dierickdie/lucy/01.1_non-snap-off/02_ori_top_plate.png

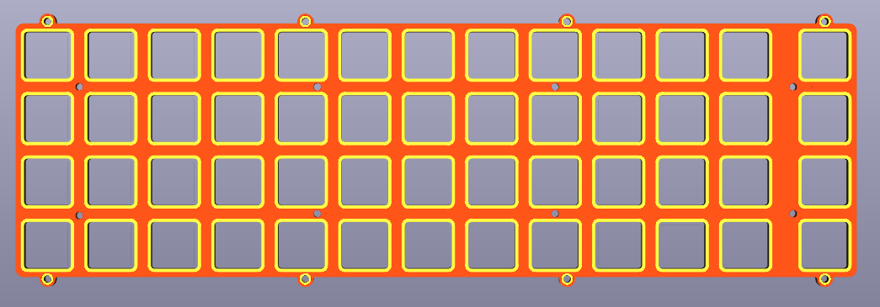
01.1_non-snap-off/02_ori_top_plate.png
