dierickdie/lucy/01_pcb/3.0-QFN-0603/footprints/AcheronLibrary-master/graphics/e6c1209rgb.png

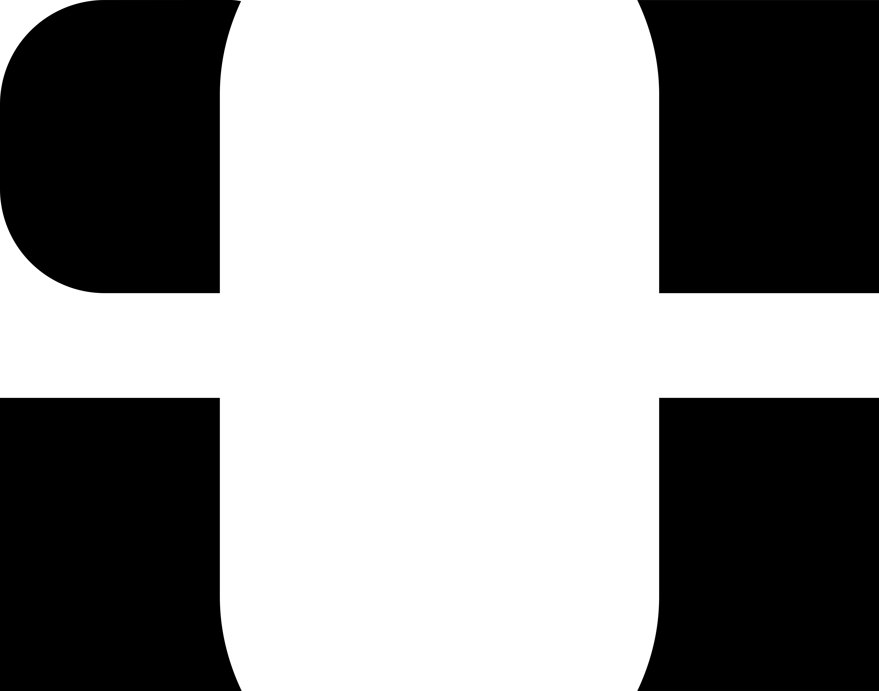
01_pcb/3.0-QFN-0603/footprints/AcheronLibrary-master/graphics/e6c1209rgb.png
