dierickdie/lucy/01_pcb/3.0-QFN-0603/footprints/AcheronLibrary-master/graphics/warning_sign.png

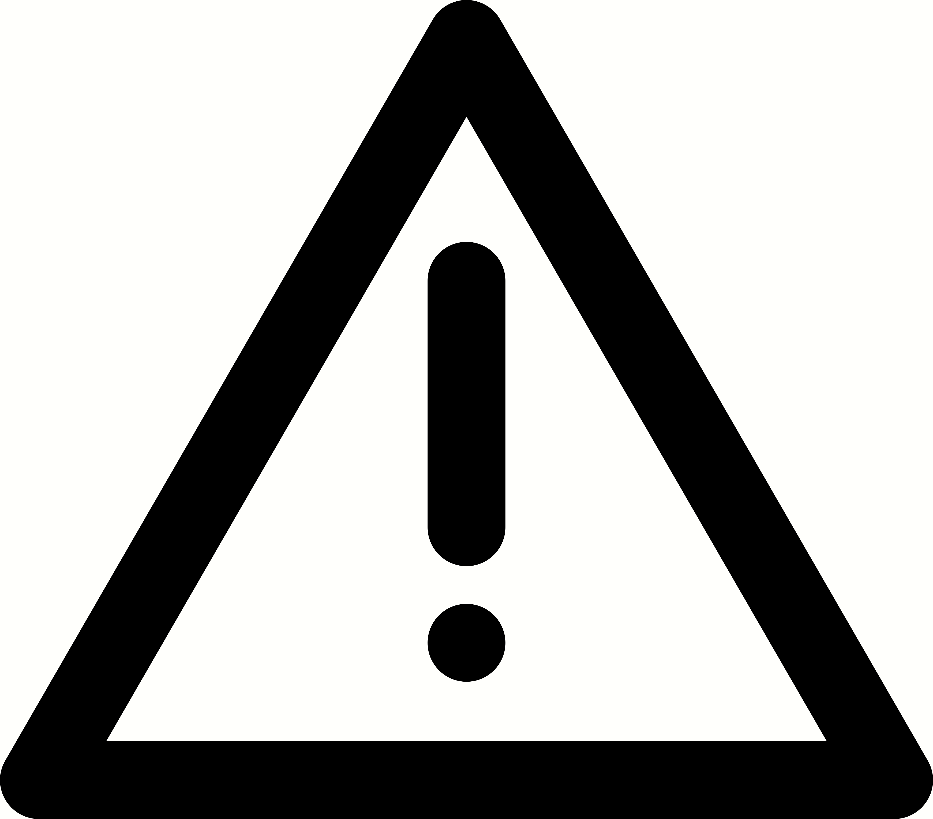
01_pcb/3.0-QFN-0603/footprints/AcheronLibrary-master/graphics/warning_sign.png
