dierickdie/lucy/01_pcb/3.0-QFN-0603/footprints/AcheronLibrary-master/svgs/halfSideHole.png

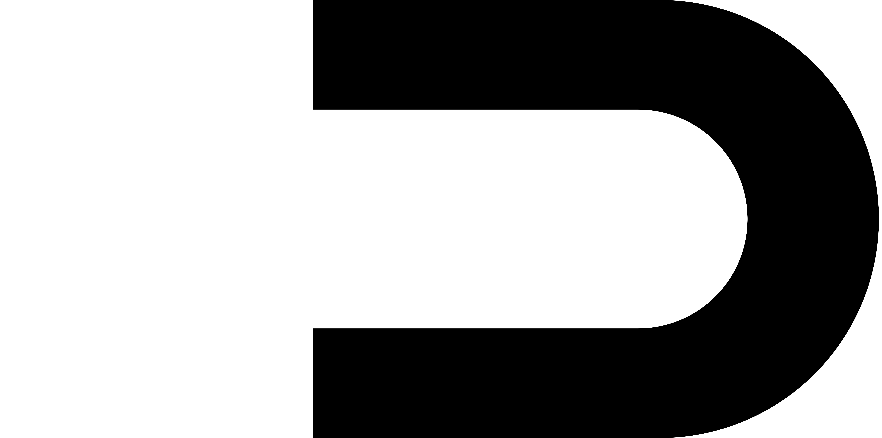
01_pcb/3.0-QFN-0603/footprints/AcheronLibrary-master/svgs/halfSideHole.png
