dierickdie/lucy/02_plate/plate.dxf

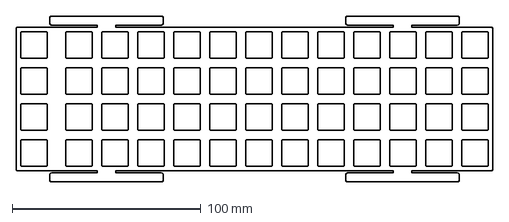
[picture p35: CAD file, 2023-03-31]
02_plate/plate.dxf
252.4 x 87.7 mm
