dierickdie/lucy/01_pcb/3.0-QFN-0603/footprints/AcheronLibrary-master/3d_models/ACM2012-2P.STEP

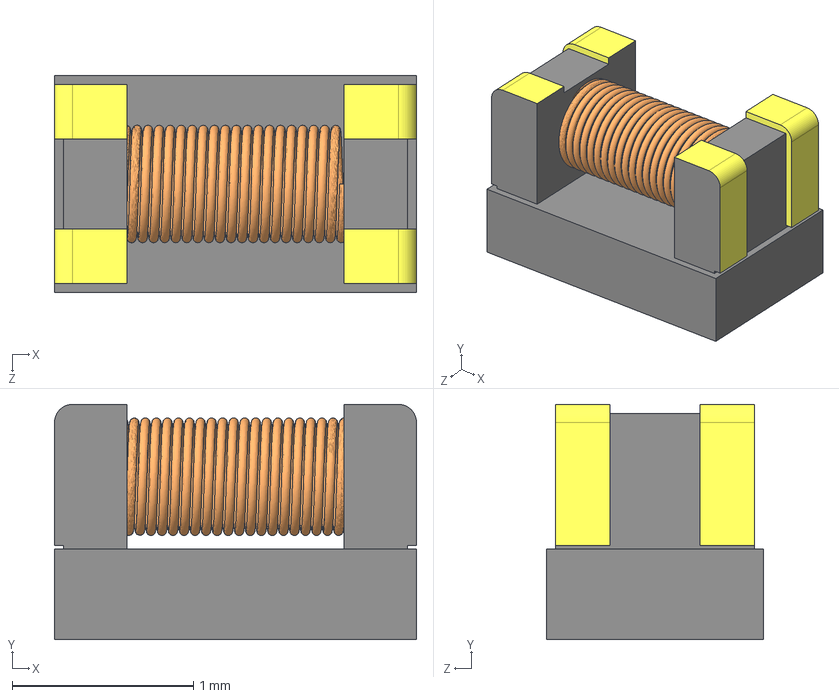
[picture p36: CAD file, 2023-03-27]
01_pcb/3.0-QFN-0603/footprints/AcheronLibrary-master/3d_models/ACM2012-2P.STEP
2.00 x 1.30 x 1.20 mm
