dierickdie/lucy/01_pcb/3.0-QFN-0603/footprints/AcheronLibrary-master/graphics/plate_cutouts/7U.dxf

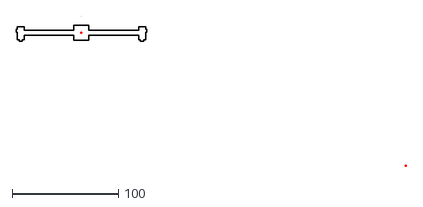
[picture p37: CAD file, 2023-03-27]
01_pcb/3.0-QFN-0603/footprints/AcheronLibrary-master/graphics/plate_cutouts/7U.dxf
367.1 x 141.8
