dierickdie/lucy/01_pcb/3.0-QFN-0603/footprints/AcheronLibrary-master/3d_models/E6C1209RGB.iges

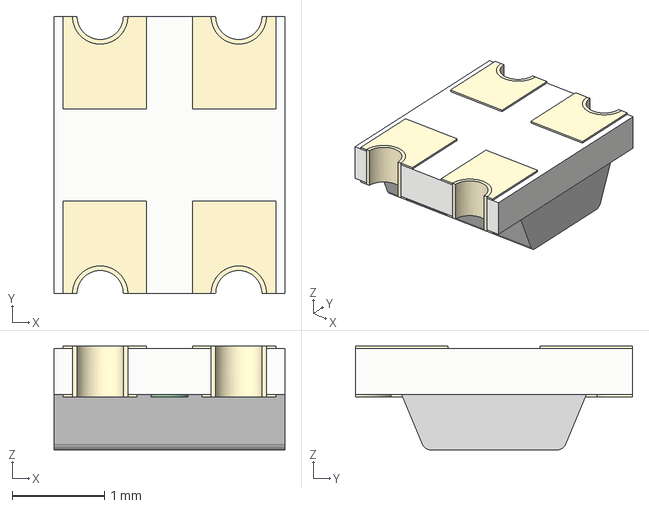
[picture p39: CAD file, 2023-03-27]
01_pcb/3.0-QFN-0603/footprints/AcheronLibrary-master/3d_models/E6C1209RGB.iges
2.50 x 3.00 x 1.12 mm
