dierickdie/lucy/01_pcb/3.0-QFN-0603/footprints/marbastlib-main/3dmodels/SW_SSSS213100.step

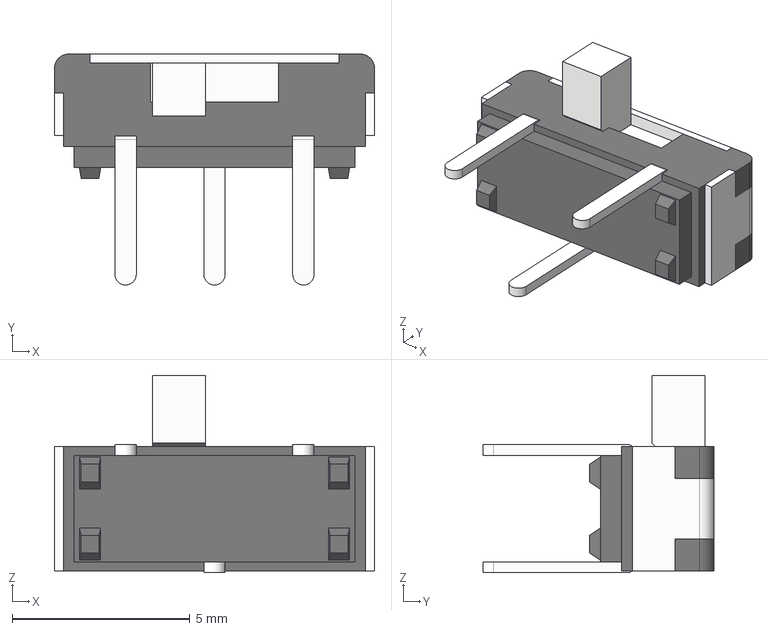
[picture p40: CAD file, 2023-04-01]
01_pcb/3.0-QFN-0603/footprints/marbastlib-main/3dmodels/SW_SSSS213100.step
9.00 x 6.50 x 5.55 mm
