dierickdie/lucy/01_pcb/3.0-QFN-0603/footprints/AcheronLibrary-master/3d_models/angle4PinHeader.step

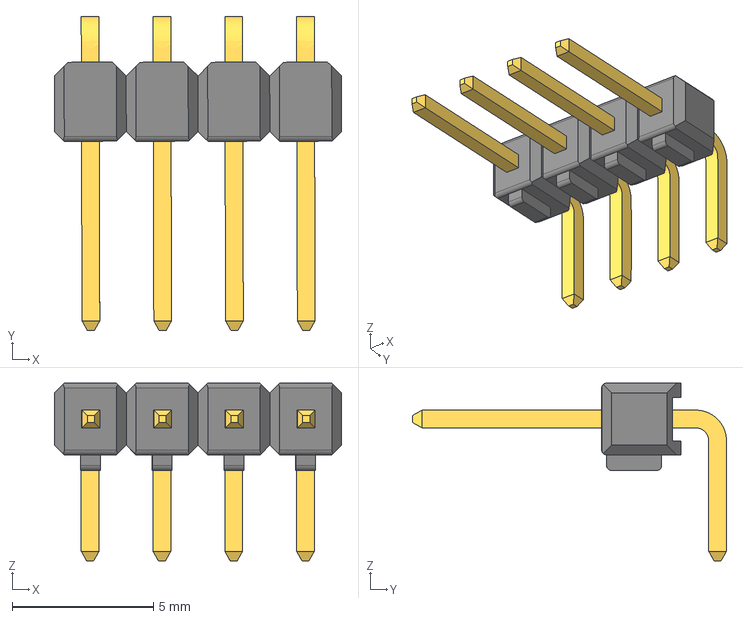
[picture p41: CAD file, 2023-03-27]
01_pcb/3.0-QFN-0603/footprints/AcheronLibrary-master/3d_models/angle4PinHeader.step
10.2 x 11.1 x 6.29 mm
