dierickdie/lucy/01_pcb/3.0-QFN-0603/footprints/AcheronLibrary-master/graphics/plate_cutouts/6.25U.dxf

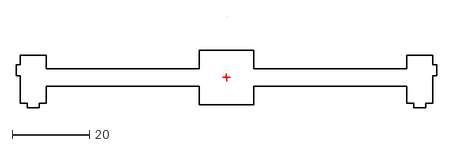
[picture p42: CAD file, 2023-03-27]
01_pcb/3.0-QFN-0603/footprints/AcheronLibrary-master/graphics/plate_cutouts/6.25U.dxf
108.6 x 23.5
