dierickdie/lucy/01_pcb/3.0-QFN-0603/footprints/marbastlib-main/3dmodels/LED_SK6812MINI-E.step

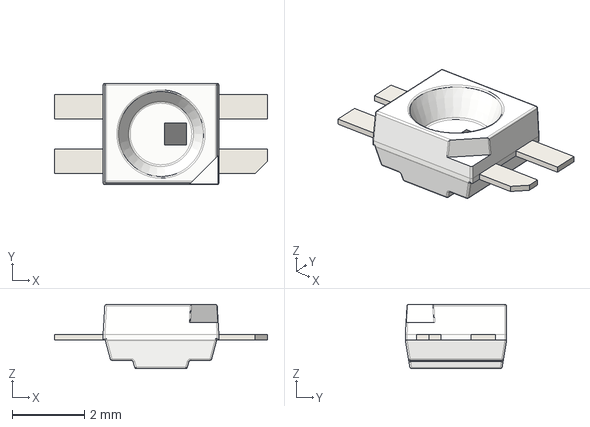
[picture p43: CAD file, 2023-04-01]
01_pcb/3.0-QFN-0603/footprints/marbastlib-main/3dmodels/LED_SK6812MINI-E.step
5.88 x 2.80 x 1.78 mm
