dierickdie/lucy/01_pcb/3.0-QFN-0603/footprints/AcheronLibrary-master/3d_models/angle6PinHeader.stp

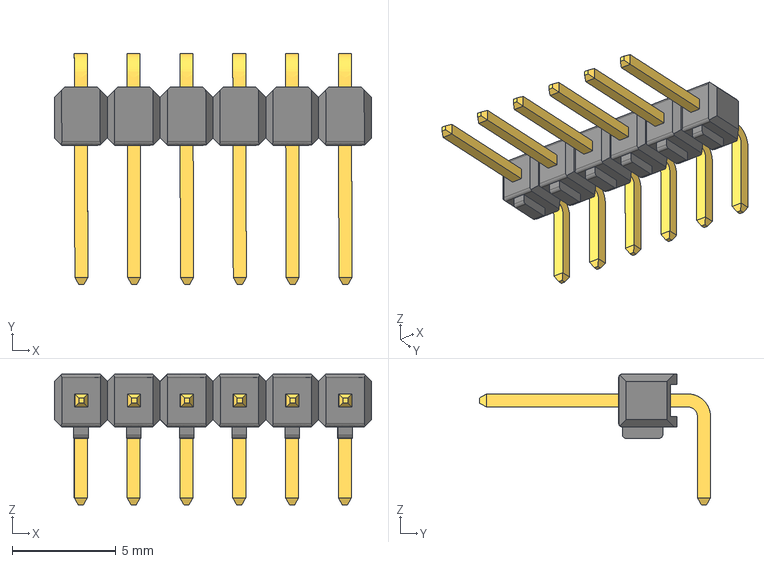
[picture p44: CAD file, 2023-03-27]
01_pcb/3.0-QFN-0603/footprints/AcheronLibrary-master/3d_models/angle6PinHeader.stp
15.2 x 11.1 x 6.29 mm
