dierickdie/lucy/01_pcb/3.0-QFN-0603/footprints/marbastlib-main/3dmodels/CON_MJ-4PP-9.step

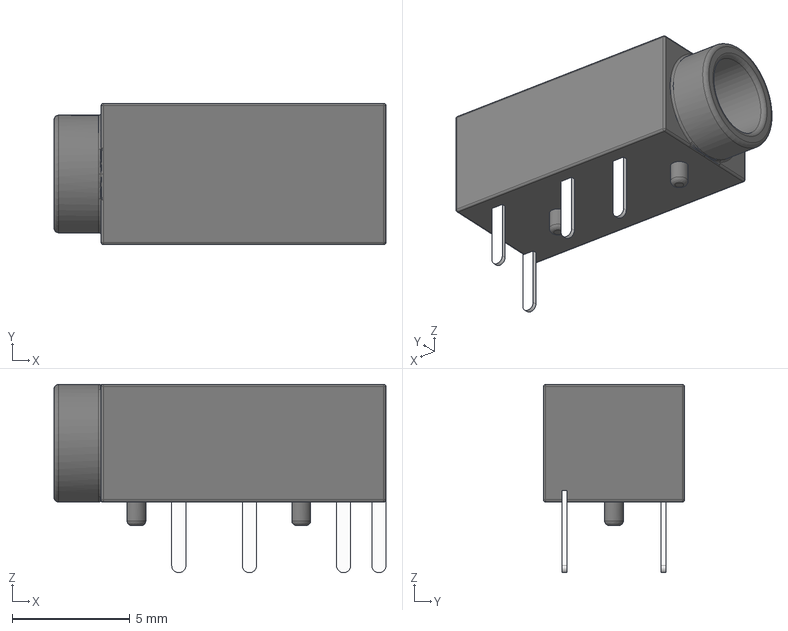
[picture p45: CAD file, 2023-04-01]
01_pcb/3.0-QFN-0603/footprints/marbastlib-main/3dmodels/CON_MJ-4PP-9.step
14.1 x 6.00 x 8.00 mm
