dierickdie/lucy/01_pcb/3.0-QFN-0603/footprints/AcheronLibrary-master/3d_models/6028SMDRGB.iges

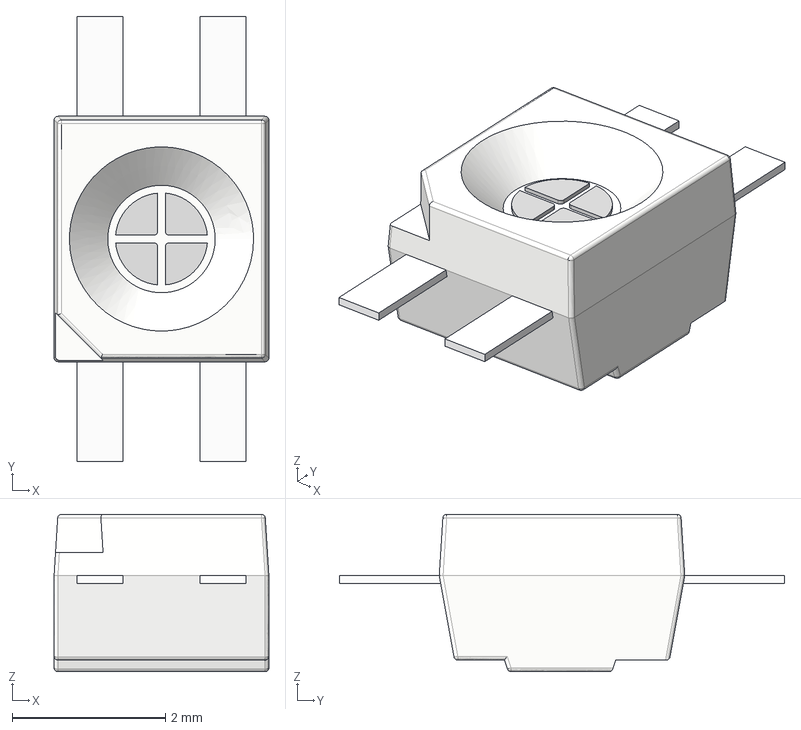
[picture p46: CAD file, 2023-03-27]
01_pcb/3.0-QFN-0603/footprints/AcheronLibrary-master/3d_models/6028SMDRGB.iges
2.80 x 5.80 x 2.05 mm
