dierickdie/lucy/01_pcb/3.0-QFN-0603/footprints/AcheronLibrary-master/3d_models/male6PinHeader.stp

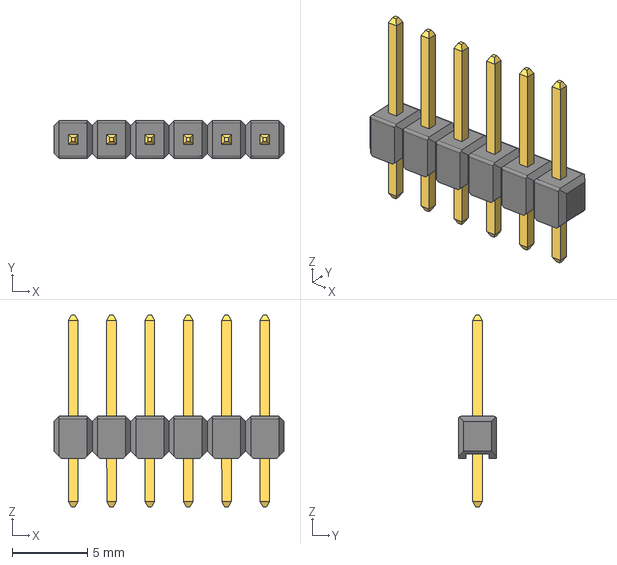
[picture p48: CAD file, 2023-03-27]
01_pcb/3.0-QFN-0603/footprints/AcheronLibrary-master/3d_models/male6PinHeader.stp
15.2 x 2.54 x 12.7 mm
