dierickdie/lucy/01_pcb/3.0-QFN-0603/footprints/marbastlib-main/3dmodels/holyiot_18010_nRF52840.step

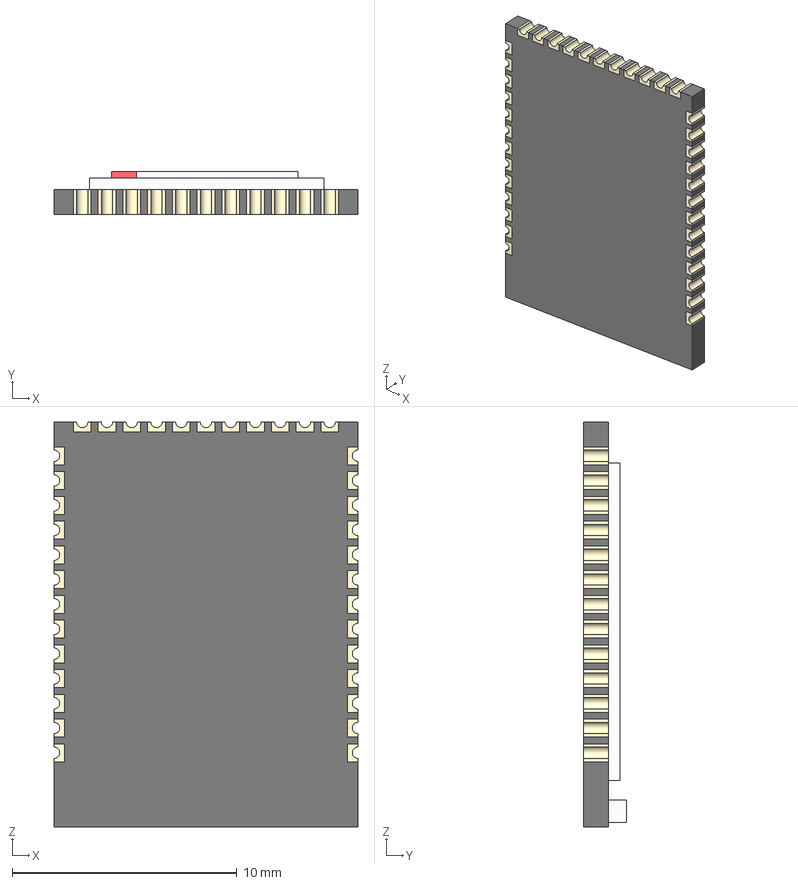
[picture p49: CAD file, 2023-04-01]
01_pcb/3.0-QFN-0603/footprints/marbastlib-main/3dmodels/holyiot_18010_nRF52840.step
13.5 x 1.92 x 18.0 mm
