dierickdie/lucy/01_pcb/3.0-QFN-0603/footprints/AcheronLibrary-master/3d_models/kailh_socket_mx.stp

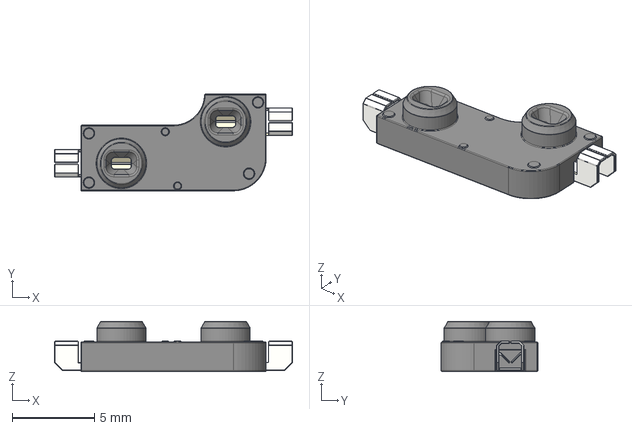
[picture p50: CAD file, 2023-03-27]
01_pcb/3.0-QFN-0603/footprints/AcheronLibrary-master/3d_models/kailh_socket_mx.stp
14.5 x 5.89 x 3.05 mm
