dierickdie/lucy/01_pcb/3.0-QFN-0603/footprints/marbastlib-main/3dmodels/PNT_psp1000.step

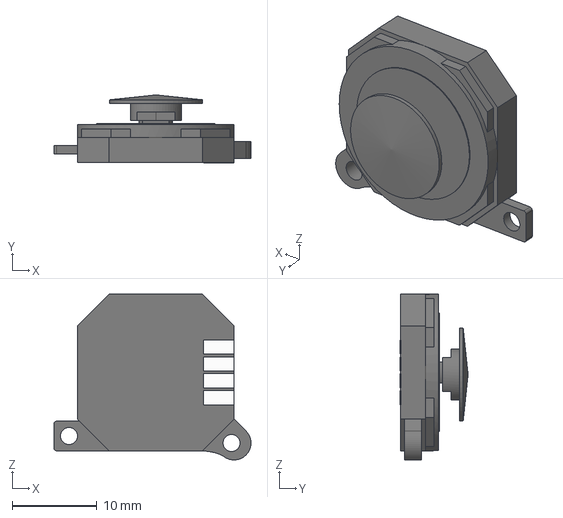
[picture p51: CAD file, 2023-04-01]
01_pcb/3.0-QFN-0603/footprints/marbastlib-main/3dmodels/PNT_psp1000.step
23.2 x 8.05 x 19.6 mm
