dierickdie/lucy/01_pcb/3.0-QFN-0603/footprints/AcheronLibrary-master/3d_models/5032_XTAL.step

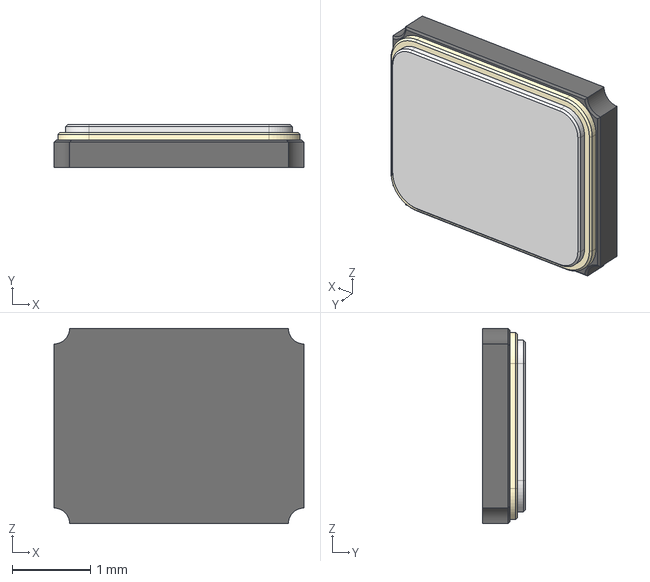
[picture p52: CAD file, 2023-03-27]
01_pcb/3.0-QFN-0603/footprints/AcheronLibrary-master/3d_models/5032_XTAL.step
3.20 x 0.55 x 2.50 mm
