dierickdie/lucy/01_pcb/3.0-QFN-0603/footprints/marbastlib-main/3dmodels/moko_mk08a_nRF52840.step

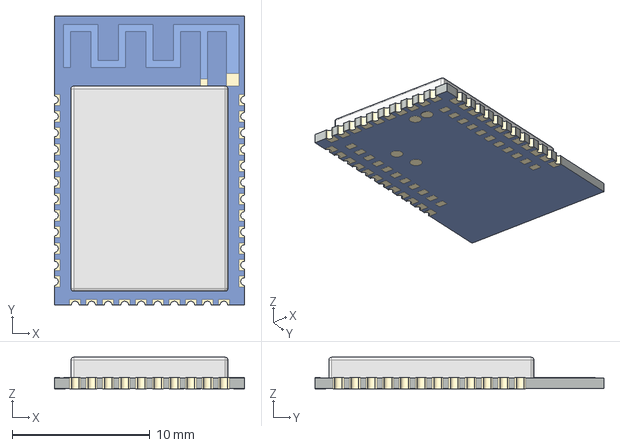
[picture p53: CAD file, 2023-04-01]
01_pcb/3.0-QFN-0603/footprints/marbastlib-main/3dmodels/moko_mk08a_nRF52840.step
13.8 x 21.0 x 2.29 mm
