dierickdie/lucy/01_pcb/3.0-QFN-0603/footprints/AcheronLibrary-master/3d_models/XM7D-0512.STEP

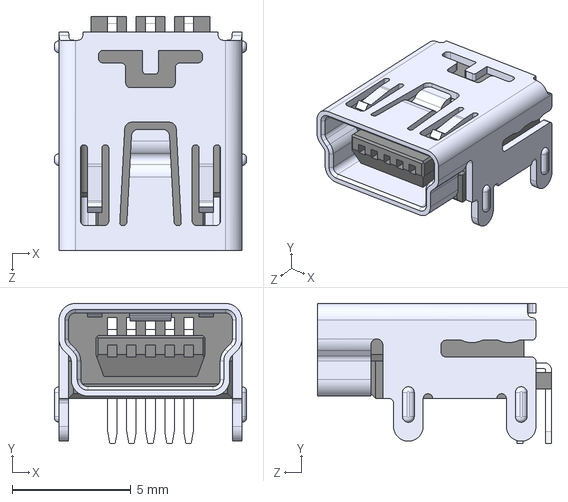
[picture p54: CAD file, 2023-03-27]
01_pcb/3.0-QFN-0603/footprints/AcheronLibrary-master/3d_models/XM7D-0512.STEP
8.10 x 5.90 x 9.85 mm
