dierickdie/lucy/01_pcb/3.0-QFN-0603/footprints/marbastlib-main/3dmodels/ROT_EC11N.step

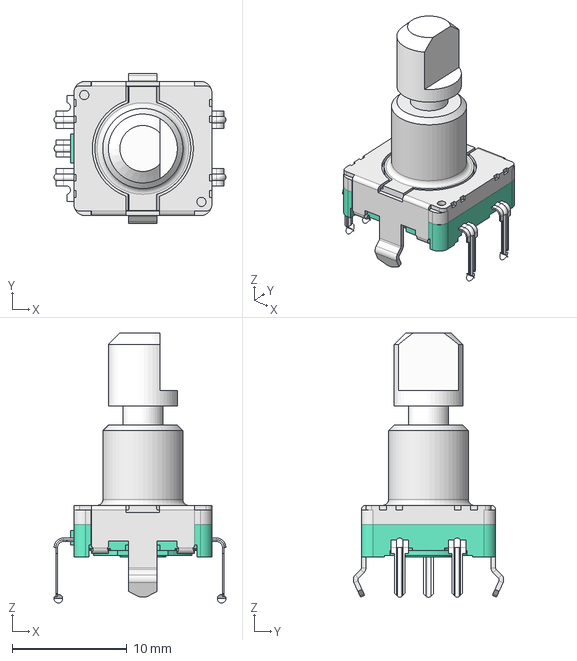
[picture p55: CAD file, 2023-04-01]
01_pcb/3.0-QFN-0603/footprints/marbastlib-main/3dmodels/ROT_EC11N.step
14.9 x 13.1 x 23.5 mm
