dierickdie/lucy/01_pcb/3.0-QFN-0603/footprints/AcheronLibrary-master/3d_models/3313J-1-202E.stp

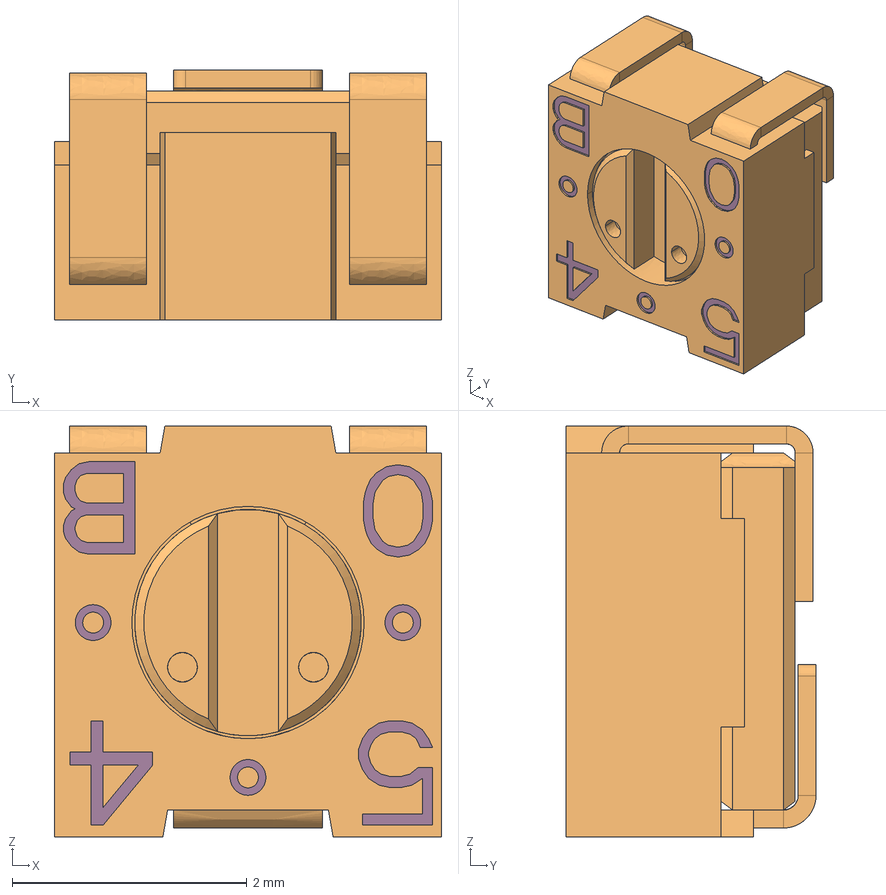
[picture p56: CAD file, 2023-03-27]
01_pcb/3.0-QFN-0603/footprints/AcheronLibrary-master/3d_models/3313J-1-202E.stp
3.30 x 2.13 x 3.51 mm
