dierickdie/lucy/01_pcb/3.0-QFN-0603/footprints/marbastlib-main/3dmodels/Crystal_FA-128.step

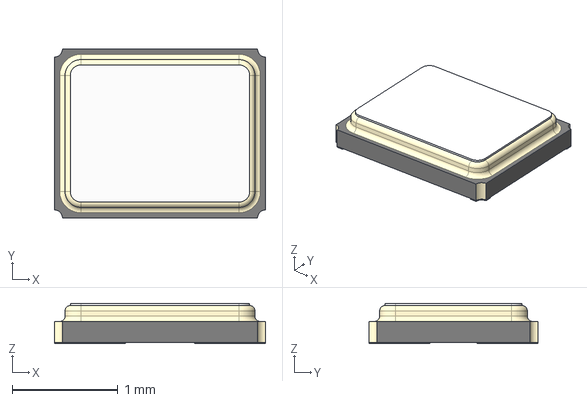
[picture p57: CAD file, 2023-04-01]
01_pcb/3.0-QFN-0603/footprints/marbastlib-main/3dmodels/Crystal_FA-128.step
2.00 x 1.60 x 0.38 mm
