dierickdie/lucy/01_pcb/3.0-QFN-0603/footprints/AcheronLibrary-master/3d_models/FUSE_1812.STEP

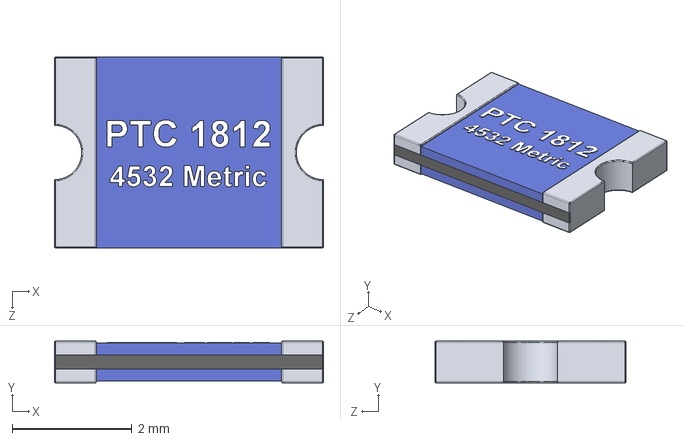
[picture p58: CAD file, 2023-03-27]
01_pcb/3.0-QFN-0603/footprints/AcheronLibrary-master/3d_models/FUSE_1812.STEP
4.50 x 0.7 x 3.20 mm
