dierickdie/lucy/01_pcb/3.0-QFN-0603/footprints/marbastlib-main/3dmodels/CON_SM02B-SRSS-TB.step

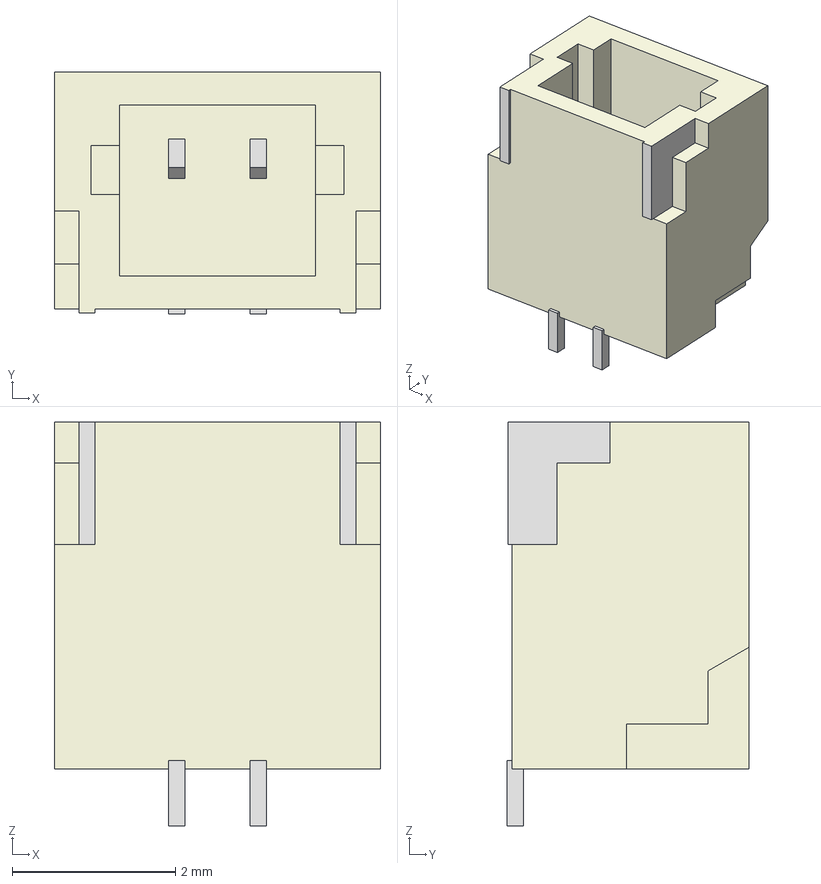
[picture p61: CAD file, 2023-04-01]
01_pcb/3.0-QFN-0603/footprints/marbastlib-main/3dmodels/CON_SM02B-SRSS-TB.step
4.00 x 2.96 x 4.95 mm
