dierickdie/lucy/01_pcb/3.0-QFN-0603/footprints/AcheronLibrary-master/3d_models/UX60SC-MB-5S8.stp

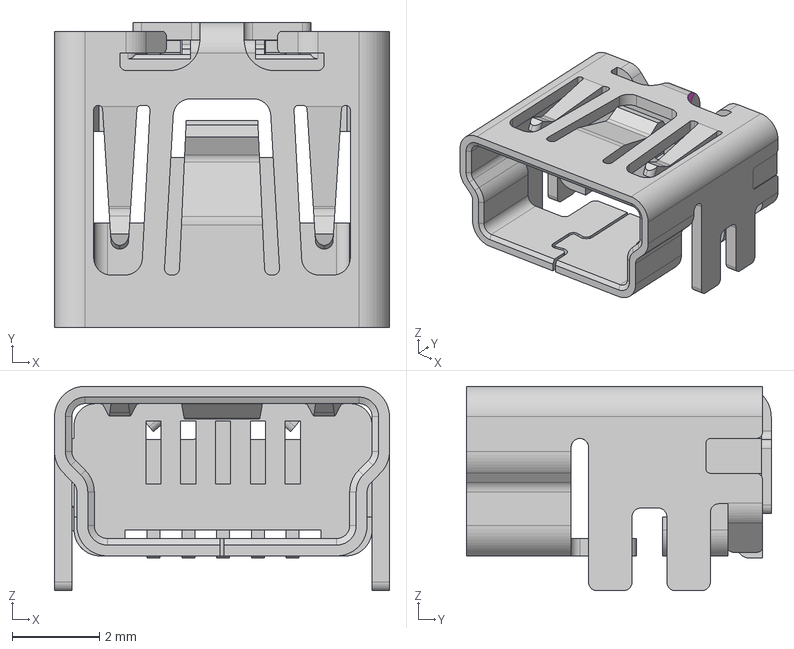
[picture p62: CAD file, 2023-03-27]
01_pcb/3.0-QFN-0603/footprints/AcheronLibrary-master/3d_models/UX60SC-MB-5S8.stp
7.70 x 7.00 x 4.70 mm
