dierickdie/lucy/01_pcb/3.0-QFN-0603/footprints/marbastlib-main/3dmodels/PNT_RKJXU1210006.step

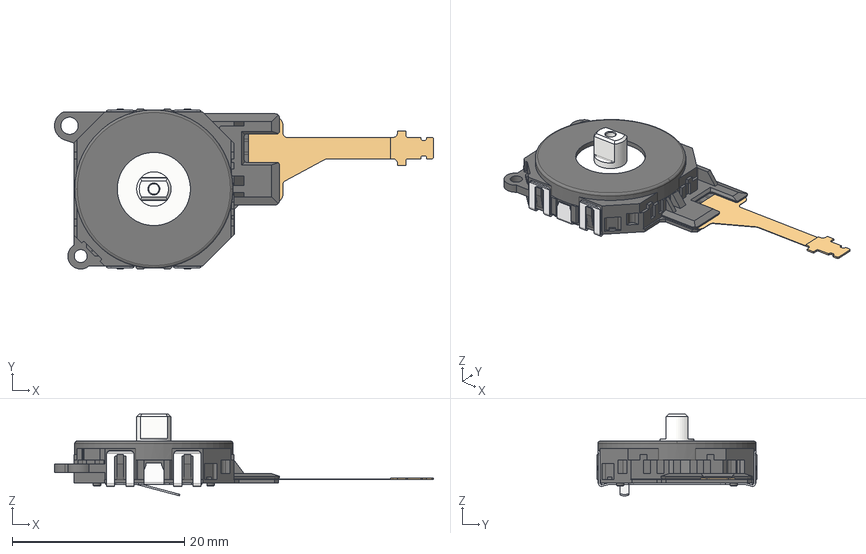
[picture p63: CAD file, 2023-04-01]
01_pcb/3.0-QFN-0603/footprints/marbastlib-main/3dmodels/PNT_RKJXU1210006.step
44.0 x 18.6 x 9.50 mm
