dierickdie/lucy/01_pcb/3.0-QFN-0603/footprints/AcheronLibrary-master/3d_models/TYPE-C-31-M-12.step

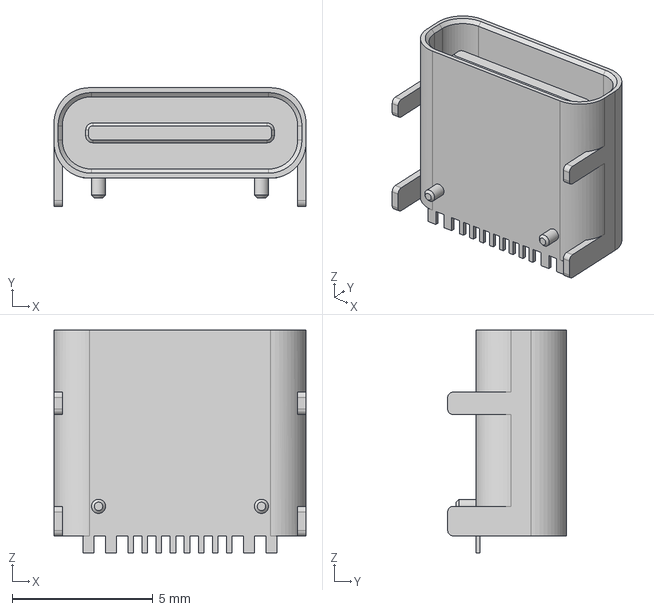
[picture p64: CAD file, 2023-03-27]
01_pcb/3.0-QFN-0603/footprints/AcheronLibrary-master/3d_models/TYPE-C-31-M-12.step
8.94 x 4.21 x 7.90 mm
