dierickdie/lucy/01_pcb/3.0-QFN-0603/footprints/marbastlib-main/3dmodels/SW_SKHLLC.step

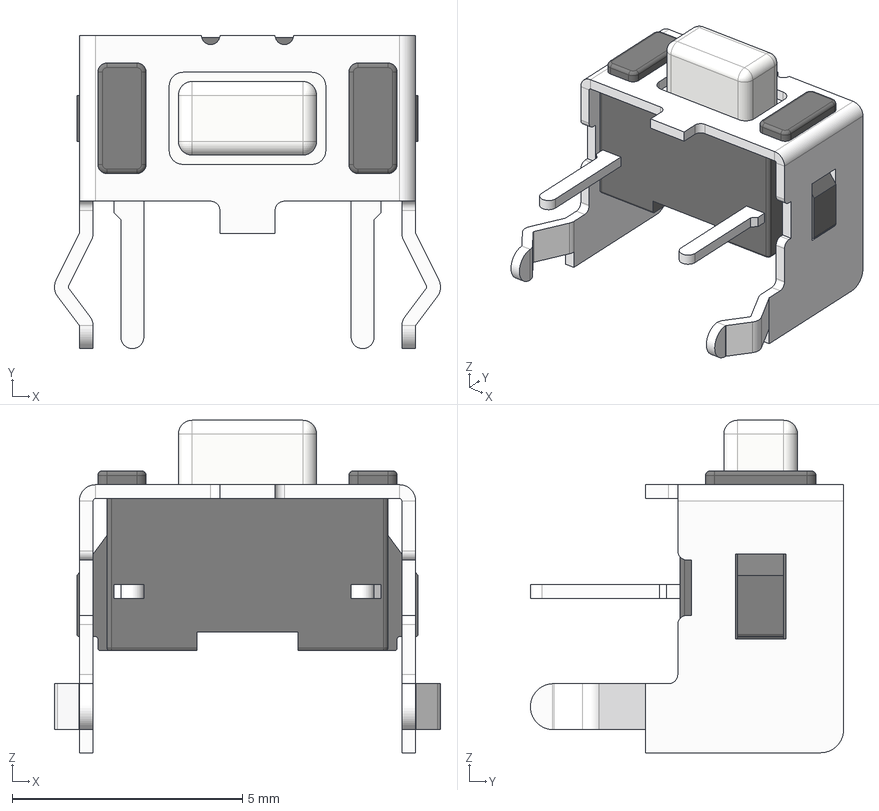
[picture p65: CAD file, 2023-04-01]
01_pcb/3.0-QFN-0603/footprints/marbastlib-main/3dmodels/SW_SKHLLC.step
8.38 x 6.80 x 7.22 mm
