dierickdie/lucy/01_pcb/3.0-QFN-0603/footprints/AcheronLibrary-master/3d_models/QFN28-P0.4mm.step

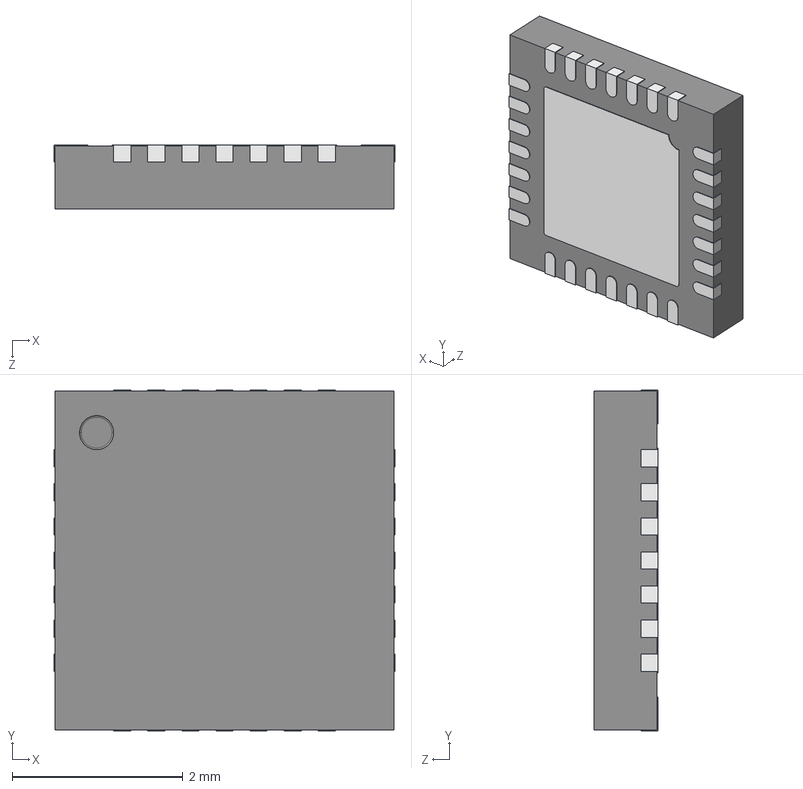
[picture p66: CAD file, 2023-03-27]
01_pcb/3.0-QFN-0603/footprints/AcheronLibrary-master/3d_models/QFN28-P0.4mm.step
4.00 x 4.00 x 0.75 mm
Free-Models
Free-Models016
Free-Models026
Free-Models027
Free-Models028
Free-Models009
Free-Models008
Free-Models007
Free-Models022
Free-Models023
Free-Models001
Free-Models003
Free-Models002
Free-Models024
Free-Models025
Free-Models014
Free-Models013
Free-Models015
Free-Models017
Free-Models018
Free-Models020
Free-Models021
Free-Models019
Free-Models005
Free-Models004
Free-Models006
Free-Models012
Free-Models011
Free-Models010
