dierickdie/lucy/01_pcb/3.0-QFN-0603/footprints/marbastlib-main/3dmodels/LED_WS2812B-MINI.step

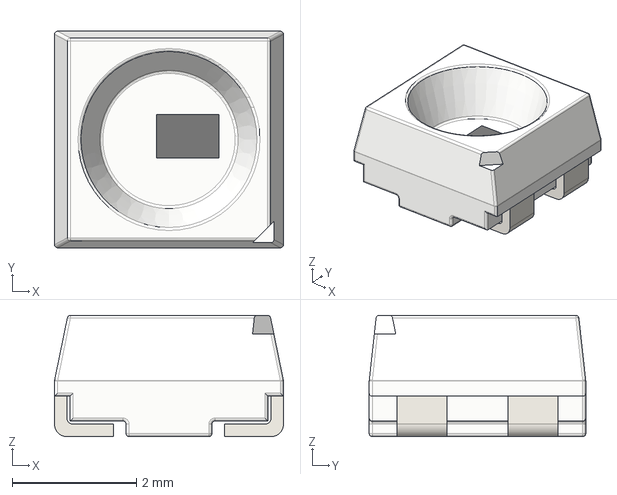
[picture p67: CAD file, 2023-04-01]
01_pcb/3.0-QFN-0603/footprints/marbastlib-main/3dmodels/LED_WS2812B-MINI.step
3.68 x 3.48 x 1.95 mm
