dierickdie/lucy/01_pcb/3.0-QFN-0603/footprints/AcheronLibrary-master/3d_models/BM04B-ASRS-TF.STEP

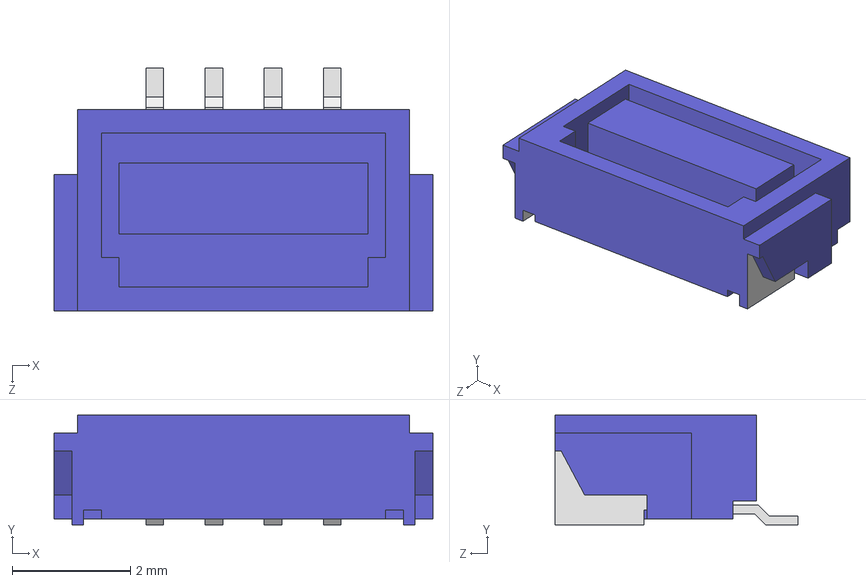
[picture p68: CAD file, 2023-03-27]
01_pcb/3.0-QFN-0603/footprints/AcheronLibrary-master/3d_models/BM04B-ASRS-TF.STEP
6.40 x 1.85 x 4.10 mm
