dierickdie/lucy/01_pcb/3.0-QFN-0603/footprints/marbastlib-main/3dmodels/LED_WS2812_2020.step

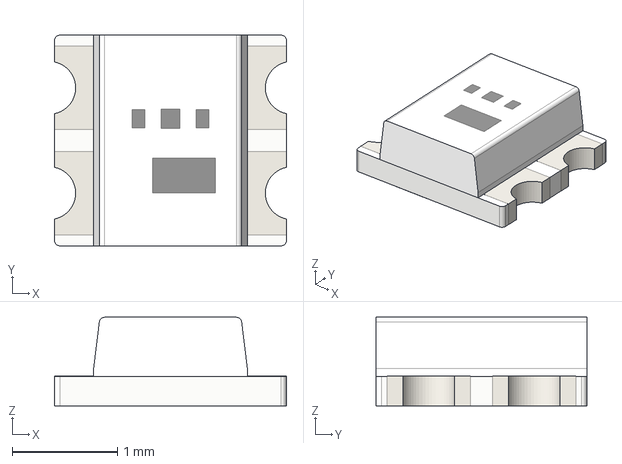
[picture p69: CAD file, 2023-04-01]
01_pcb/3.0-QFN-0603/footprints/marbastlib-main/3dmodels/LED_WS2812_2020.step
2.20 x 2.00 x 0.842 mm
