dierickdie/lucy/01_pcb/3.0-QFN-0603/footprints/AcheronLibrary-master/3d_models/ALPS_EC11E.stp

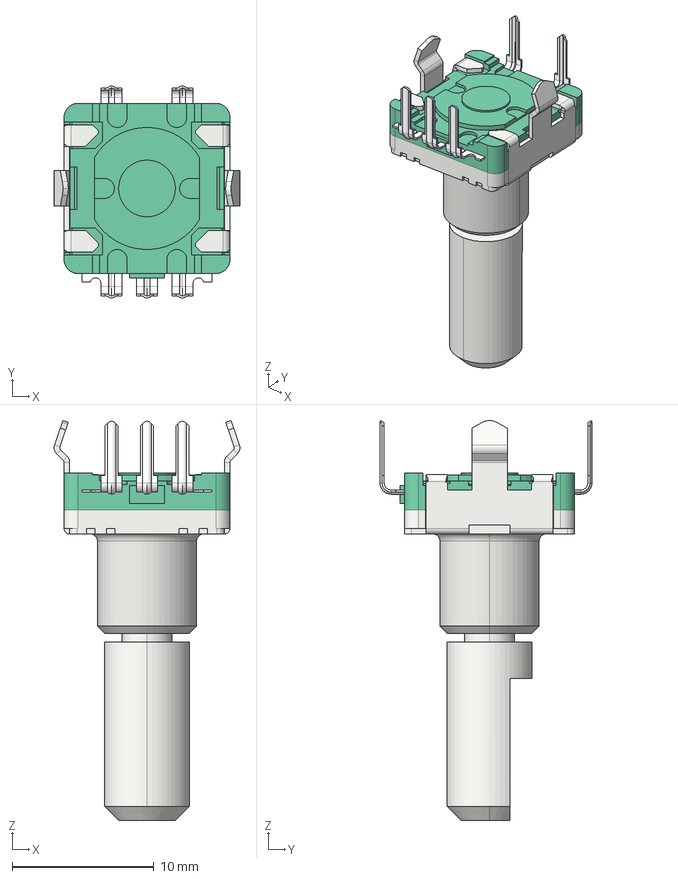
[picture p70: CAD file, 2023-03-27]
01_pcb/3.0-QFN-0603/footprints/AcheronLibrary-master/3d_models/ALPS_EC11E.stp
13.1 x 15.0 x 28.2 mm
