dierickdie/lucy/01_pcb/3.0-QFN-0603/footprints/marbastlib-main/3dmodels/SW_SSSS223900.step

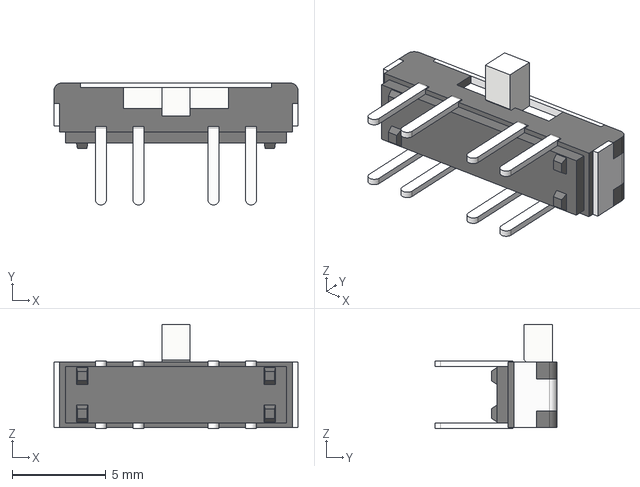
[picture p71: CAD file, 2023-04-01]
01_pcb/3.0-QFN-0603/footprints/marbastlib-main/3dmodels/SW_SSSS223900.step
13.0 x 6.50 x 5.55 mm
