dierickdie/lucy/01_pcb/3.0-QFN-0603/footprints/AcheronLibrary-master/3d_models/OSC5032.STEP

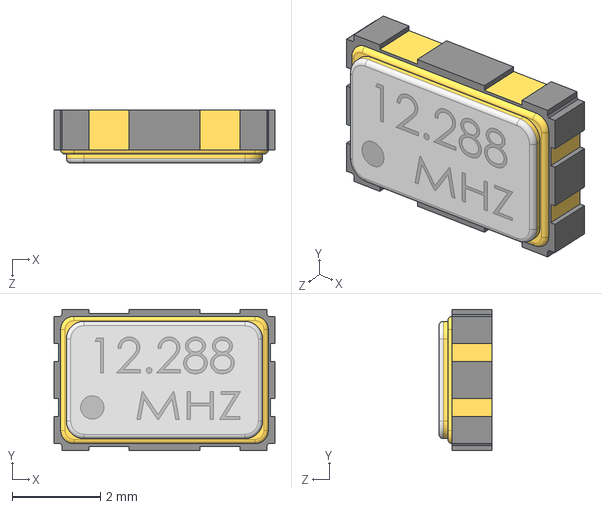
[picture p74: CAD file, 2023-03-27]
01_pcb/3.0-QFN-0603/footprints/AcheronLibrary-master/3d_models/OSC5032.STEP
5.00 x 3.20 x 1.20 mm
