dierickdie/lucy/01_pcb/3.0-QFN-0603/footprints/marbastlib-main/3dmodels/SW_MSK12C02.step

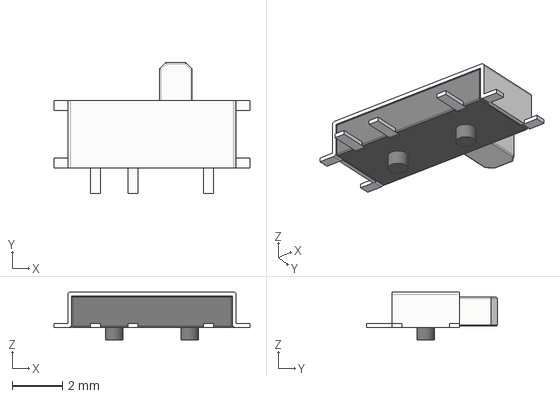
[picture p77: CAD file, 2023-04-01]
01_pcb/3.0-QFN-0603/footprints/marbastlib-main/3dmodels/SW_MSK12C02.step
7.80 x 5.20 x 1.90 mm
