dierickdie/lucy/01_pcb/3.0-QFN-0603/footprints/marbastlib-main/3dmodels/CON_BM02B-ACHSS.step

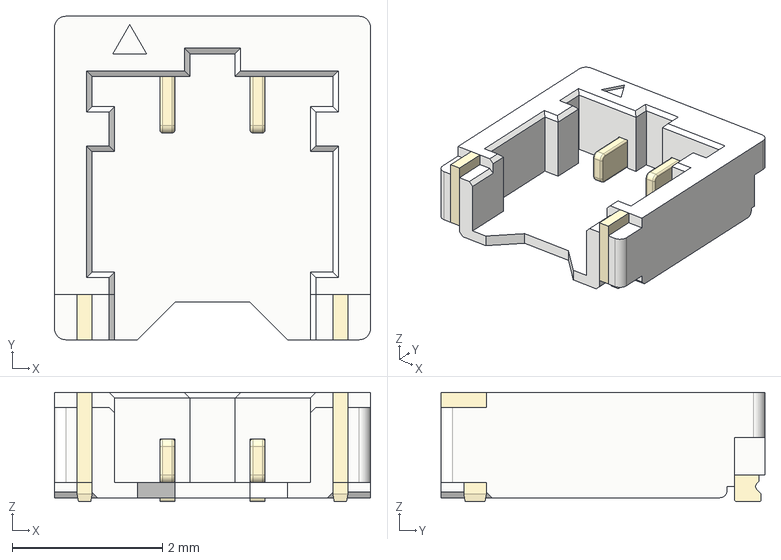
[picture p78: CAD file, 2023-04-01]
01_pcb/3.0-QFN-0603/footprints/marbastlib-main/3dmodels/CON_BM02B-ACHSS.step
4.20 x 4.30 x 1.45 mm
