dierickdie/lucy/01_pcb/3.0-QFN-0603/footprints/marbastlib-main/3dmodels/SW_ESP3020.step

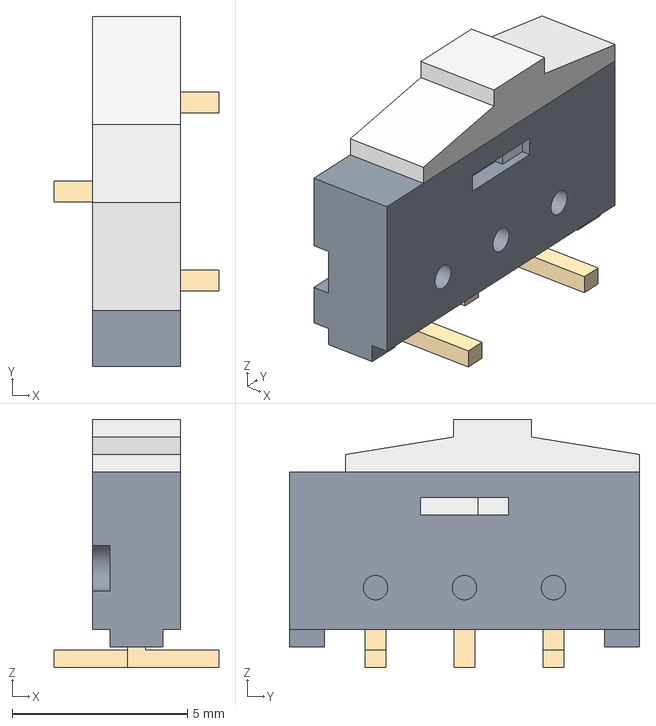
[picture p79: CAD file, 2023-04-01]
01_pcb/3.0-QFN-0603/footprints/marbastlib-main/3dmodels/SW_ESP3020.step
4.70 x 10.0 x 7.08 mm
