dierickdie/lucy/01_pcb/3.0-QFN-0603/footprints/marbastlib-main/3dmodels/ROT_EC11E.step

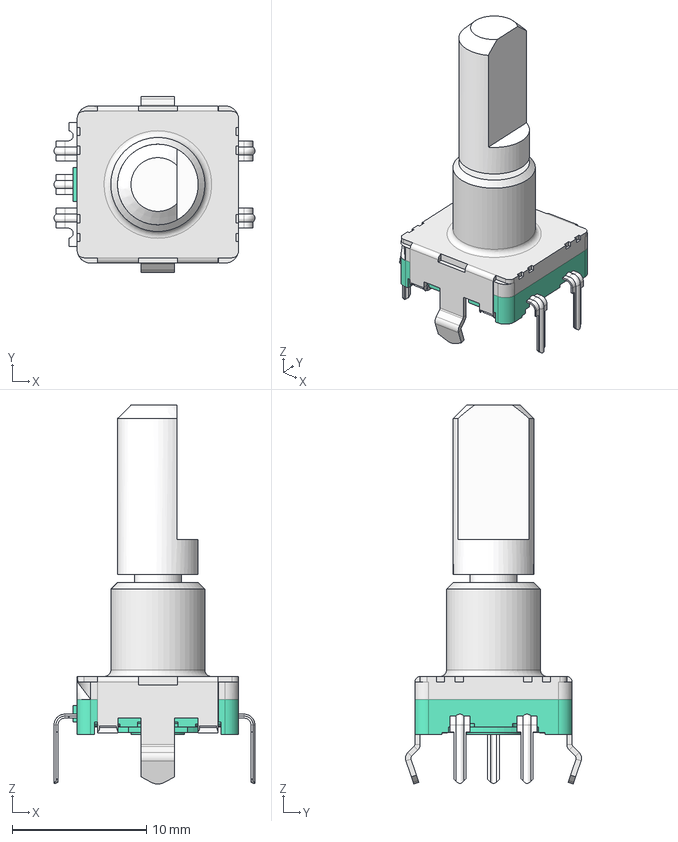
[picture p80: CAD file, 2023-04-01]
01_pcb/3.0-QFN-0603/footprints/marbastlib-main/3dmodels/ROT_EC11E.step
14.9 x 13.1 x 28.2 mm
