dierickdie/lucy/01_pcb/3.0-QFN-0603/footprints/marbastlib-main/3dmodels/HS_Kailh_MX.step

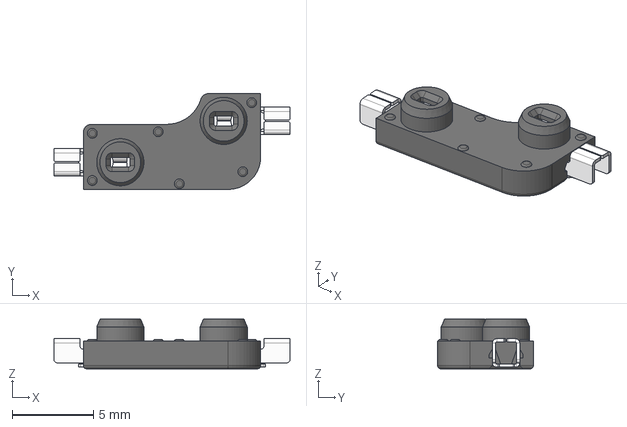
[picture p81: CAD file, 2023-04-01]
01_pcb/3.0-QFN-0603/footprints/marbastlib-main/3dmodels/HS_Kailh_MX.step
14.5 x 5.89 x 3.05 mm
Contact x 2
