dierickdie/lucy/01_pcb/3.0-QFN-0603/footprints/marbastlib-main/3dmodels/HS_Kailh_Choc.step

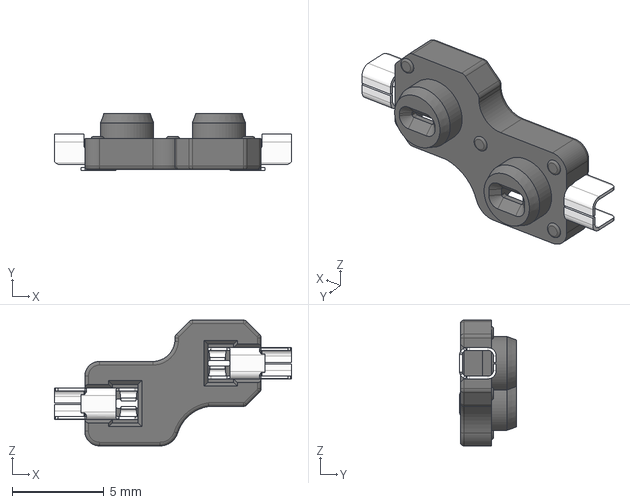
[picture p84: CAD file, 2023-04-01]
01_pcb/3.0-QFN-0603/footprints/marbastlib-main/3dmodels/HS_Kailh_Choc.step
12.9 x 3.09 x 6.85 mm
pin x 2
socket
