dierickdie/lucy/01_lucy/lucy.sch

## KiCad design 01_lucy/lucy.sch (2021-10-08)

Schematic: lucy.sch

Parts:
C1, C2, C3: .1uF; C_0805_2012Metric_Pad1.15x1.40mm_HandSolder
C5: 10uF; C_0805_2012Metric_Pad1.15x1.40mm_HandSolder
C6: 1uF; C_0805_2012Metric_Pad1.15x1.40mm_HandSolder
CX1, CX2: 22pF; C_0805_2012Metric_Pad1.15x1.40mm_HandSolder
D1, D2, D3, D4, D5, D6, D7, D8, D9, D10, D11, D12, D13, D14, D15, D16, D17, D18, D19, D20, D21, D22, D23, D24, D25, D26, D27, D28, D29, D30, D31, D32, D33, D34, D35, D36, D37, D38, D39, D40, D41, D42, D43, D44, D45, D46, D47, D48, D49, D50, D51, D52: D; D_SOD-123_modified
F1: .5A; Fuse_0805_2012Metric_Pad1.15x1.40mm_HandSolder
J1: TYPE-C-31-M12_13; TYPE-C-31-M-12
J2: AVR-ISP-6_mod; PIN_HEADER_1x6_OFFSET
K1, K2, K3, K4, K5, K6, K7, K8, K9, K10, K11, K12, K13, K14, K15, K16, K17, K18, K19, K20, K21, K22, K23, K24, K25, K26, K27, K28, K29, K30, K31, K32, K33, K34, K35, K36, K37, K38, K39, K40, K41, K42, K43, K44, K45, K46, K47, K48, K49, K50, K51, K52: KEYSW; MX100
LED1: LED; LED_0805_2012Metric_Pad1.15x1.40mm_HandSolder
R1: 10k; R_0805_2012Metric_Pad1.15x1.40mm_HandSolder
R2, R3: 22; R_0805_2012Metric_Pad1.15x1.40mm_HandSolder
R4: 1k; R_0805_2012Metric_Pad1.15x1.40mm_HandSolder
RCC1, RCC2: 5.1k; R_0805_2012Metric_Pad1.15x1.40mm_HandSolder
RSW1: 10k; R_0805_2012Metric_Pad1.15x1.40mm_HandSolder
SW1: SW_PUSH; SKQG-1155865
SW2: Rotary_Encoder_Switch; RotaryEncoder_EC11
U1: ATMEGA32U4; ATMEGA32U4-AU
U2: PRTR5V0U2X; SOT-143B
Y1: 16MHz; Crystal_SMD_3225-4Pin_3.2x2.5mm_HandSoldering

Notes on the sheet:
Crystal
VCC Capacitors
Power LED
ISP Flashing
ESD Protection
